cclaunch/Virtual2315/FPGA verilog source/spi_interface.v

//==========================================================================================================
// RK05 Emulator
// Processor SPI Interface
// File Name: spi_interface.v
// Functions: 
//   read and write FPGA hardware control registers.
//   read and write SDRAM data.
//   write SDRAM address register for processor SDRAM accesses.
// Modified for 2310 by Carl Claunch
//
//==========================================================================================================

module spi_interface(
    input wire clock,                    // master clock 40 MHz
    input wire reset,                    // active high synchronous reset input
    input wire spi_clk,                  // SPI clock
    input wire spi_cs_n,                 // SPI active low chip select
    input wire spi_mosi,                 // SPI controller data output, peripheral data input
    input wire [15:0] dram_readdata,     // 16-bit read data from DRAM controller
    input wire [7:0] Cylinder_Address,   // input to be able to read the Cylinder Address
    input wire Head_Select,              // input to be able to read the Head Select bit
    input wire Selected_Ready,           // input to be able to read Selected_Ready
    input wire [1:0] Sector_Address,     // Sector Address to be read test visibility mode
    input wire strobe_selected_ready,
    input wire read_selected_ready,
    input wire write_selected_ready,
    input wire BUS_UNLOCKED_EMUL_L,      // driven by drive_select.v
    input wire BUS_FILE_READY_CTRL_L,    // we say the drive is ready for input output operations
    input wire BUS_WRITE_SEL_ERR_L,      // got error trying to select/write on drive
    input wire ECC_error,                // got error in four ECC bits during write
    input wire real_drive,               // hybrid or pure virtual mode
    output reg spi_miso,                 // SPI controller data input, peripheral data output
    output reg load_address_spi,         // enable from SPI to command the sdram controller to load address 8 bits at a time
    output reg [7:0] spi_serpar_reg,     // 8-bit serpar register used for writing to the sdram address register
    output reg dram_read_enbl_spi,       // read enable request to DRAM controller
    output reg dram_write_enbl_spi,      // write enable request to DRAM controller
    output reg [15:0] dram_writedata_spi,// 16-bit write data to DRAM controller
    output reg Cart_Ready,               // disk contents have been copied from the microSD to the SDRAM.
    output reg Read_Only,                // CPU register that indicates no writeback of updates to cartridge at shutdown
    output reg Fault_Latch,              // combines faults detected in Pico handling uSD files plus drive fault
    output reg Reset_Cylinder,           // drive powered down causes arm retract to cylinder 0
    output reg command_interrupt
);

//============================ Internal Connections ==================================

//`define EMULATOR_FPGA_CODE_VERSION  8'h51  // hex number that indicates the version of the FPGA code

reg [7:0] spiserialreg;
reg [3:0] metaspi;
reg dramwrite_lowhigh;
reg dramread_lowhigh;
reg [4:0] spicount; // define as 5 bits instead of 4 to prevent the first bit from wrapping around at the end of transmitting the 16-bit data (8 addr + 8 data)
reg [7:0] serialaddress;
wire [7:0] muxed_read_data;
wire pre_spi_miso;
reg toggle_wp;
reg [1:0] operation_id;
reg Disk_Fault;
reg [15:0] saveread;
reg [3:0] armcount;

wire spi_start;

//============================ Start of Code =========================================

// SB_DFFS - D Flip-Flop, Set is asynchronous to the clock
SB_DFFS SPI_DFFS_inst (
.Q(spi_start), // Registered Output, "Q" output of the DFF
.C(~spi_clk),  // rising-edge Clock, so with ~spi_clk as the input, Q changes on the falling edge of spi_clk
.D(1'b0),      // Data, clocks in a zero on the falling edge of spi_clk
.S(spi_cs_n)   // Asynchronous active-high Set, we perform async set of the DFF while spi_cs_n is inactive
);


// produce inputs to registers we will write up to the Pico when it does a read of these reg address
// these readback have diff # assigned to them, thus reading 03 is done with reg address A0
// others just read out internal state, eg. 81 grabs current cylinder address
assign muxed_read_data = (serialaddress == 8'h81) 
                         ?  Cylinder_Address[7:0] 
                         :  (serialaddress == 8'h82) 
                            ?  {2'b0, Sector_Address[1:0], operation_id[1:0], Selected_Ready, Head_Select} 
                            : (serialaddress == 8'ha0) 
                              ?  {Read_Only, ~BUS_FILE_READY_CTRL_L,Disk_Fault, Cart_Ready, ~BUS_UNLOCKED_EMUL_L, ECC_error, 1'd0, real_drive}
                              :  (serialaddress == 8'h88) 
                                 ?  (dramread_lowhigh)
                                    ?  saveread[15:8] 
                                    :  saveread[7:0]
                                 : 8'b0;

// 81 returns the current cylinder address

// 82 returns the sector address, head select, 
//    what operation triggered the command_interrupt, and write_selected_ready

// 88 reads a byte of one word from SDRAM, two calls gives us one word from SDRAM
//   dram_readdata[15:0] always has the data ready that was read at the dram_address.
//   The DRAM word read function is triggered after the odd byte is read.
//   The next word is requested after reading the high byte from register 0x88.

// A0 reads back status similar to what is set by 00
//    x80 is Read_Only
//    x40 is File Ready set by FPGA and lamp lit by Pico
//    x20 is Fault_Latch set by FPGA and lamp lit by Pico
//    x10 is Cart Ready set in FPGA by Pico and lamp lit by Pico
//    x08 is Unlocked when 1, set in FPGA and lamp controlled by Pico
//    x04 is ECC_error condition from the last write operation
//    x02 is 1 of the 3 bit drive select value from Pico, now 0
//    x01 is real drive mode, 1 means hybrid using physical drive

// 03 sets Cart_Ready to bit x10 value

// 04 sets Read Only state to bit x01 value

// 05 sent three times with upper, middle and lower part of memory address

// 06 sent twice to write high and low half of memory word

// 10 sets flag to reset the Cylinder_Address to zero from bit x01

// 88 sent twice to read high and low halves of memory word

assign pre_spi_miso = ((spicount == 5'd7) & muxed_read_data[7]) | 
                      ((spicount == 5'd8) & muxed_read_data[6]) |
                      ((spicount == 5'd9) & muxed_read_data[5]) |
                      ((spicount == 5'd10) & muxed_read_data[4]) |
                      ((spicount == 5'd11) & muxed_read_data[3]) |
                      ((spicount == 5'd12) & muxed_read_data[2]) |
                      ((spicount == 5'd13) & muxed_read_data[1]) |
                      ((spicount == 5'd14) & muxed_read_data[0]);

always @ (posedge spi_clk)
begin : SPICLKPOSFUNCTIONS // block name
  // Reset the SPI bit counter using the DFF that is set when spi_cs_n is inactive
  // The SPI bit counter is used by a mux to serialize the SPI read data.
  spicount <= spi_start ? 5'd0 : spicount + 1;
  serialaddress <= (spicount == 6) ? {spiserialreg[6:0], spi_mosi} : serialaddress;

  if(spi_cs_n == 1'b0) begin
    spiserialreg[7:0] <= {spiserialreg[6:0], spi_mosi};
  end
  else begin
    spiserialreg[7:0] <= 8'hff;
  end
end

always @ (negedge spi_clk)
begin : SPICLKNEGFUNCTIONS // block name
  spi_miso <= pre_spi_miso;
end

always @ (posedge spi_cs_n)
begin : SPICSPOSFUNCTIONS // block name
    spi_serpar_reg <=  spiserialreg;
end

always @ (posedge clock)
begin : HSCLOCKFUNCTIONS // block name
  if(reset == 1'b1) begin
    dram_read_enbl_spi <= 1'b0;
    dram_write_enbl_spi <= 1'b0;
    Cart_Ready <= 1'b0;
    Read_Only <= 1'b0;
    Fault_Latch <= 1'b0;
    Reset_Cylinder <= 1'b0;
    load_address_spi <= 1'b0;
    dramwrite_lowhigh <= 1'b0;
    dramread_lowhigh <= 1'b0;
    dram_writedata_spi <= 16'd0;
    metaspi <= 4'b0000;
    toggle_wp <= 1'b0;
    operation_id <= 2'b00;
    command_interrupt <= 1'b0;
    Disk_Fault <= 1'b0;
    saveread <= 16'd0;
    armcount <= 4'd0;
  end
  else begin

    Disk_Fault <= real_drive == 1'b1
                 ?  ~BUS_WRITE_SEL_ERR_L | ECC_error  // actual fault from drive or bad ECC bits on write
                 :  ECC_error;                        // bad ECC bits on write
    
    command_interrupt <= strobe_selected_ready || read_selected_ready || write_selected_ready;

    operation_id <= strobe_selected_ready 
                  ? 2'h0 
                  : (read_selected_ready 
                         ? 2'h1 
                         : (write_selected_ready 
                                 ? 2'h2 
                                 : operation_id));


    metaspi[3:0] <= {metaspi[2:0], ~spi_cs_n};

    // fault latch set on when Disk_Fault is on
    // and turned off when disk is not ready to 1130
    Fault_Latch <= BUS_FILE_READY_CTRL_L == 1'b1
                   ? 1'b0
                   : Disk_Fault == 1'b1
                     ? 1'b1
                     : Fault_Latch;

  //
  // below for register address 0x03 when written by the Pico
  //
    // x10 is Cart Ready set/clear by Pico
    Cart_Ready <=        ((serialaddress == 8'h03) && ~metaspi[2] && metaspi[3]) 
                 ? spi_serpar_reg[4]   
                 : Cart_Ready; 

  //
  // below for register x04 which records the read only condition, controlling the LED
  //
    //toggle_wp is separated only so the code is more readable
    toggle_wp <= (serialaddress == 8'h04) && ~metaspi[2] && metaspi[3] && spi_serpar_reg[0] 
                 ? 1'b1
                 : 1'b0;

    // Q <= (Q | Set) & ~Reset
    // Set when (toggle_wp & ~Q)
    // Reset when (toggle_wp & Q)
    Read_Only <= (Read_Only | ((toggle_wp & ~Read_Only))) & ~((toggle_wp & Read_Only));
 
  //
  // below for register address 0x05 written by Pico
  //
    // x05 sets memory address via three sequential messages
    load_address_spi   <= (serialaddress == 8'h05) & ~metaspi[2] & metaspi[3]; // command to load 8 bits of address from SPI

  //
  // below for register address 0x06 written by Pico
  //
    // register address 0x06 written by Pico sends data word via pair of sequential messages
    dram_writedata_spi[7:0] <=  ((serialaddress == 8'h06) && ~metaspi[2] && metaspi[3]) 
                             ? dram_writedata_spi[15:8] 
                             : dram_writedata_spi[7:0];
    dram_writedata_spi[15:8] <= ((serialaddress == 8'h06) && ~metaspi[2] && metaspi[3]) 
                              ? spi_serpar_reg 
                              : dram_writedata_spi[15:8];
    dram_write_enbl_spi <=       (serialaddress == 8'h06) & ~metaspi[2] & metaspi[3] & dramwrite_lowhigh;

  //
  // below for register address 0x10 written by Pico
  // used to zero the cylinder address
  //
    // x10 sets reset flag on or off
    Reset_Cylinder  <= (serialaddress == 8'h10) & ~metaspi[2] & metaspi[3]
                       ? spi_serpar_reg[0]
                       : Reset_Cylinder;

  //
  // below for register 0x88 retrieves words from memory via pair of sequential messages
  //
    // register address 0x88 written by Pico triggers read on second (low) 88 message
    // dram_readdata[15:0] always has the data ready that was read at the dram_address.
    // The read function is triggered after the odd byte is read.
    // The next word is requested after reading bits 7 to 0 when the SPI address is 8'h88.
    // Save the data from the read associated with load_address_spi 8 cycles later
    // toggle respective lowhigh bits on a write or read, clear both bits on address load, otherwise lowhigh bits remain the same
    dram_read_enbl_spi <= (serialaddress == 8'h88) & ~metaspi[2] & metaspi[3] & ~dramread_lowhigh;
    armcount           <= (serialaddress == 8'h05) & ~metaspi[2] & metaspi[3]
                          ?  4'd10
                          :  armcount == 4'd0
                             ?  armcount
                             :  armcount - 1;

    saveread           <= (serialaddress == 8'h88) & ~metaspi[2] & metaspi[3] & dramread_lowhigh 
                          ?  dram_readdata
                          :  armcount == 4'd1 
                             ?  dram_readdata
                             :  saveread;

  //
  // below for dramwrite_lowhigh and dramread_lowhigh toggled so pairs of 06 or 88 messages cause a single read or write
  //
    // dram_readdata[15:0] always has the data ready that was read at the dram_address.
    // The read function is triggered after the odd byte is read.
    // The next word is requested after reading the high byte when the SPI address is 8'h88.
    // toggle respective lowhigh bits on a write or read, clear both bits on address load, otherwise lowhigh bits remain the same
    dramwrite_lowhigh <= ((serialaddress == 8'h06) && ~metaspi[2] && metaspi[3]) 
                       ? ~dramwrite_lowhigh 
                       : (((serialaddress == 8'h05) && ~metaspi[2] && metaspi[3]) 
                               ? 1'b0 
                               : dramwrite_lowhigh);
    dramread_lowhigh  <= ((serialaddress == 8'h88) && ~metaspi[2] && metaspi[3]) 
                       ? ~dramread_lowhigh 
                       : (((serialaddress == 8'h05) && ~metaspi[2] && metaspi[3]) 
                               ? 1'b0 
                               : dramread_lowhigh);
  end
end // End of Block HSCLOCKFUNCTIONS

endmodule // End of Module spi_interface
