cclaunch/Virtual2315/PICO C source/display_big_images.h

// *********************************************************************************
// display_big_images.h
//   bitmap arrays of large drive address digits, digit pairs, and various other bitmaps
// *********************************************************************************
// 

// converted the bmp files using https://lvgl.io/tools/imageconverter
//   Color format: CF_INDEXED_1_BIT
//   Output format: C array
//   Options: none
//
unsigned char digit_0m[] = {
  0x00, 0x00, 0x00, 0x00, 0x00, 0xf0, 0x00, 0x00, 0x00, 0x00, 
  0x00, 0x00, 0x00, 0x00, 0x0f, 0xff, 0x00, 0x00, 0x00, 0x00, 
  0x00, 0x00, 0x00, 0x00, 0x3f, 0xff, 0xc0, 0x00, 0x00, 0x00, 
  0x00, 0x00, 0x00, 0x00, 0x7f, 0xff, 0xe0, 0x00, 0x00, 0x00, 
  0x00, 0x00, 0x00, 0x00, 0xff, 0xff, 0xf0, 0x00, 0x00, 0x00, 
  0x00, 0x00, 0x00, 0x01, 0xff, 0xff, 0xf0, 0x00, 0x00, 0x00, 
  0x00, 0x00, 0x00, 0x01, 0xff, 0xff, 0xf8, 0x00, 0x00, 0x00, 
  0x00, 0x00, 0x00, 0x03, 0xfe, 0x07, 0xf8, 0x00, 0x00, 0x00, 
  0x00, 0x00, 0x00, 0x03, 0xfc, 0x07, 0xfc, 0x00, 0x00, 0x00, 
  0x00, 0x00, 0x00, 0x07, 0xf8, 0x03, 0xfc, 0x00, 0x00, 0x00, 
  0x00, 0x00, 0x00, 0x07, 0xf8, 0x03, 0xfc, 0x00, 0x00, 0x00, 
  0x00, 0x00, 0x00, 0x07, 0xf0, 0x01, 0xfc, 0x00, 0x00, 0x00, 
  0x00, 0x00, 0x00, 0x07, 0xf0, 0x01, 0xfe, 0x00, 0x00, 0x00, 
  0x00, 0x00, 0x00, 0x0f, 0xf0, 0x01, 0xfe, 0x00, 0x00, 0x00, 
  0x00, 0x00, 0x00, 0x0f, 0xf0, 0x01, 0xfe, 0x00, 0x00, 0x00, 
  0x00, 0x00, 0x00, 0x0f, 0xf0, 0x01, 0xfe, 0x00, 0x00, 0x00, 
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
  0x00, 0x00, 0x00, 0x00, 0x00, 0x00, 0x00, 0x00, 0x00, 0x00, 
  0x00, 0x00, 0x00, 0x00, 0x00, 0x00, 0x00, 0x00, 0x00, 0x00, 
  0x00, 0x00, 0x00, 0x00, 0x00, 0x00, 0x00, 0x00, 0x00, 0x00, 
  0x00, 0x00, 0x00, 0x00, 0x00, 0x00, 0x00, 0x00, 0x00, 0x00, 
};
