cclaunch/Virtual2315/FPGA verilog source/bus_outputs.v

//==========================================================================================================
// RK05 Emulator
// Bus Outputs Logic
// File Name: bus_outputs.v
// Functions: 
//   Translate internal signals to the polarity of the 2310 outputs.
//   Output polarity is switchable so any open collector chip can be used
//   Gate all outputs with the internal Selected and Ready signal.
//
// Modified by Carl V Claunch to emulate the IBM 2310
//
//==========================================================================================================

module bus_outputs (
    input wire Selected,                  // active high signal indicates that the drive is selected
    input wire Fault_Latch,               // included for future support. Software will always write zero to Fault_Latch.
    input wire Cart_Ready,                // PICO says we are ready to do input output operations
    input wire real_drive,                // do we have physical drive in hybrid mode or all virtual 
    input wire BUS_FILE_READY_L,          // real drive is ready, heads loaded
    input wire BUS_WRITE_SEL_ERR_L,       // error when attempting write
    input wire BUS_90S_RELAY_L,           // 90 second relay while drive purges
    input wire BUS_ACCESS_RDY_EMUL_H,     // indicates at track zero
    input wire BUS_HOME_DRIVE_EMUL_L,     // indicates at track zero
    input wire BUS_WT_CLOCKB_EMUL_L,      // 720 KHz clock to control writes
    input wire BUS_SECTOR_EMUL_H,         // 165 us positive pulse each time a sector slot passes the transducer
    input wire BUS_INDEX_EMUL_H,          // 165 us positive pulse for each revolution of the disk, 600 μs after the sector pulse
    input wire BUS_90SEC_RELAY_EMUL_L,    // 90 second relay while drive purges
    input wire BUS_RD_DATA_H,             // output of read module
    input wire BUS_RD_CLK_H,              // output of read module
    input wire clock,                     // FPGA clock
    output reg BUS_10_20_DRIVE_L,         // seek step size, one or two tracks
    output reg BUS_ACC_GO_DRIVE_DRIVE_L,  // Strobe to enable movement
    output reg BUS_ACC_REV_DRIVE_L,       // direction of seek, forward or reverse
    output reg BUS_HEAD_SELECT_DRIVE_L,   // Head Select
    output reg BUS_RD_GATE_DRIVE_L,       // Read gate, when active enables read circuitry
    output reg BUS_WT_GATE_DRIVE_L,       // Write gate, when active enables write circuitry
    output reg BUS_WT_DATA_CLK_DRIVE_L,   // Composite write data and write clock
    output reg BUS_ACCESS_RDY_CTRL_H,     // Seek ready and on-cylinder
    output reg BUS_HOME_CTRL_L,           // indicates at track zero
    output reg BUS_WT_CLOCKB_CTRL_L,      // 720 KHz clock to control writes
    output reg BUS_RD_DATA_CTRL_L,        // Read data pulses, 160 ns pulse
    output reg BUS_RD_CLK_CTRL_L,         // Read clock pulses, 160 ns pulse
    output reg BUS_FILE_READY_CTRL_L,     // data copied from microSD to SDRAM, drive is ready, heads loaded
    output reg BUS_SECTOR_CTRL_L,         // 160 us negative pulse each time a sector slot passes the transducer
    output reg BUS_INDEX_CTRL_L,          // 160 us negative pulse for each revolution of the disk, 600 μs after the sector pulse
    output reg BUS_WRITE_SEL_ERR_CTRL_L,  // error when attempting write
    output reg BUS_90S_RELAY_CTRL_L,      // 90 second relay while drive purges
    output reg Selected_Ready             // disk contents have been copied from the microSD to the SDRAM & drive selected & ~fault latch
);

//============================ Local Data =========================================


//============================ Start of Code =========================================

always @ (posedge clock)
begin : BUSOUTPUTS // block name


    // we are always selected. virtual mode needs cartridge loaded from SD card, 1130 controller indicating File Ready and no fault
    Selected_Ready                     <=   real_drive == 1'b1
                                                ? 1'b1
                                                : Selected & Cart_Ready & ~Fault_Latch;

    // Signals that don't depend on real_drive status, pass along to drive
    BUS_ACC_GO_DRIVE_DRIVE_L       <=         1'b1;
    BUS_10_20_DRIVE_L              <=         1'b1;
    BUS_ACCESS_RDY_CTRL_H          <=      real_drive == 1'b1
                                             ? 1'b1
                                             : (BUS_ACCESS_RDY_EMUL_H & Cart_Ready);
    BUS_HOME_CTRL_L                <=      real_drive == 1'b1
                                             ? 1'b1
                                             : (BUS_HOME_DRIVE_EMUL_L | ~Cart_Ready);
    BUS_SECTOR_CTRL_L              <=      real_drive == 1'b1
                                             ? 1'b1
                                             : ~(BUS_SECTOR_EMUL_H | ~Cart_Ready);
    BUS_INDEX_CTRL_L               <=      real_drive == 1'b1
                                             ? 1'b1
                                             : ~(BUS_INDEX_EMUL_H | ~Cart_Ready);
    BUS_ACC_REV_DRIVE_L            <=        1'b1;

    // signals sent to 1130 regardless of mode
    BUS_WT_CLOCKB_CTRL_L           <=        (BUS_WT_CLOCKB_EMUL_L | ~Cart_Ready);
    BUS_RD_DATA_CTRL_L             <=        (~BUS_RD_DATA_H);
    BUS_RD_CLK_CTRL_L              <=        (~BUS_RD_CLK_H);

    // never sent to drive
    BUS_HEAD_SELECT_DRIVE_L        <=        1'b1;
    BUS_RD_GATE_DRIVE_L            <=        1'b1;
    BUS_WT_GATE_DRIVE_L            <=        1'b1;
    BUS_WT_DATA_CLK_DRIVE_L        <=        1'b1;


    // Signals that depend on real_drive status
    BUS_WRITE_SEL_ERR_CTRL_L       <=        real_drive == 1'b1
                                               ? (BUS_WRITE_SEL_ERR_L)
                                               : 1'b1;
    
    BUS_90S_RELAY_CTRL_L           <=        real_drive == 1'b1   // don't pass along if we are not ready to go
                                               ? (BUS_90S_RELAY_L & Selected_Ready)
                                               : (BUS_90SEC_RELAY_EMUL_L | ~Cart_Ready);

    BUS_FILE_READY_CTRL_L          <=        real_drive == 1'b1
                                               ? (BUS_FILE_READY_L | ~Cart_Ready)        
                                               : (~Cart_Ready | ~Selected);


end // End of Block BUSOUTPUTS

endmodule // End of Module bus_outputs
