cclaunch/Virtual2315/PICO C source/emulator_command.cpp

// *********************************************************************************
// emulator_command.cpp
//  implementation of command parsing and execution of commands that apply to the
//  emulator Interface Test Mode
// 
// *********************************************************************************
// 
#include <stdio.h>
#include "pico/stdlib.h"
#include <string.h>

#include "disk_state_definitions.h"
//#include "display_functions.h"
//#include "display_timers.h"
#include "emulator_hardware.h"
#include "microsd_file_ops.h"
#include "display_functions.h"

#include "emulator_global.h"
